Ductapemaster/HondaFitHDMI/wiki/hu_internals/original/pcb_audio_bottom.jpg

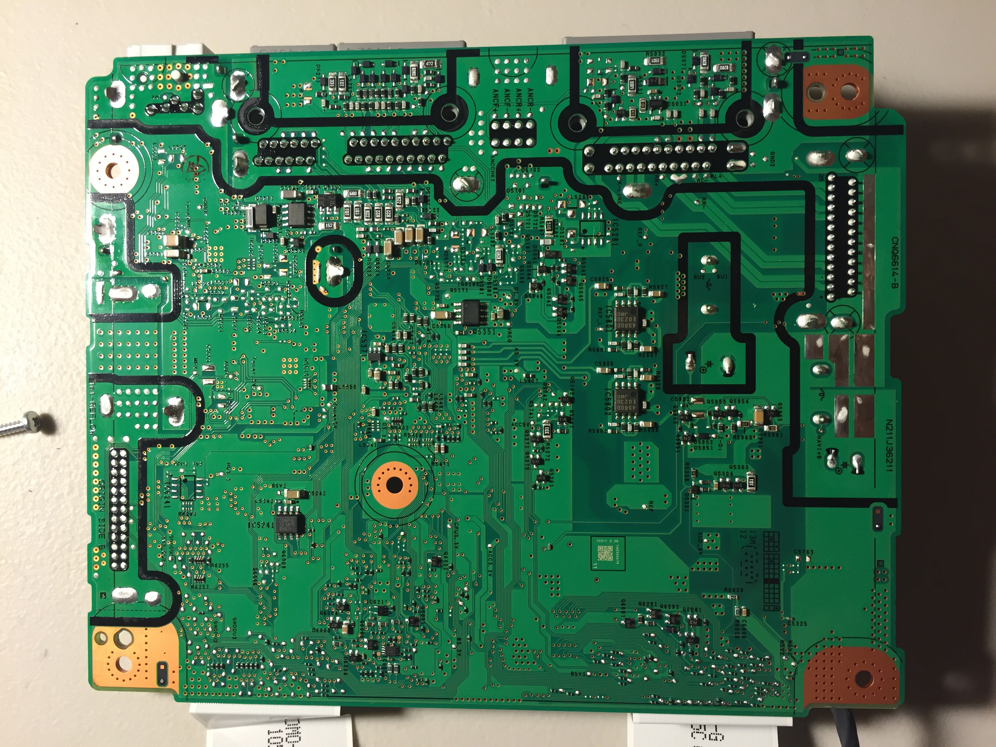
wiki/hu_internals/original/pcb_audio_bottom.jpg
