Ductapemaster/HondaFitHDMI/wiki/hu_internals/original/pcb_cpu_bottom.JPG

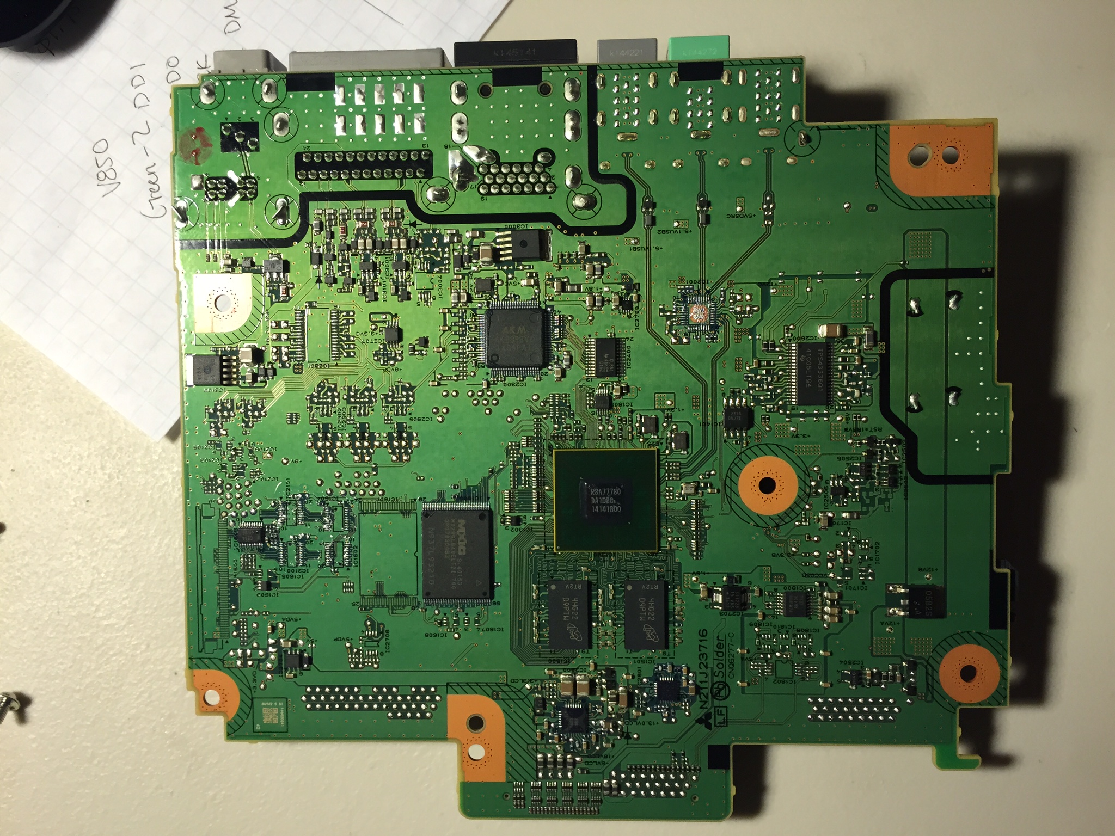
wiki/hu_internals/original/pcb_cpu_bottom.JPG
