Ductapemaster/HondaFitHDMI/wiki/hu_internals/original/pcb_cpu_top.JPG

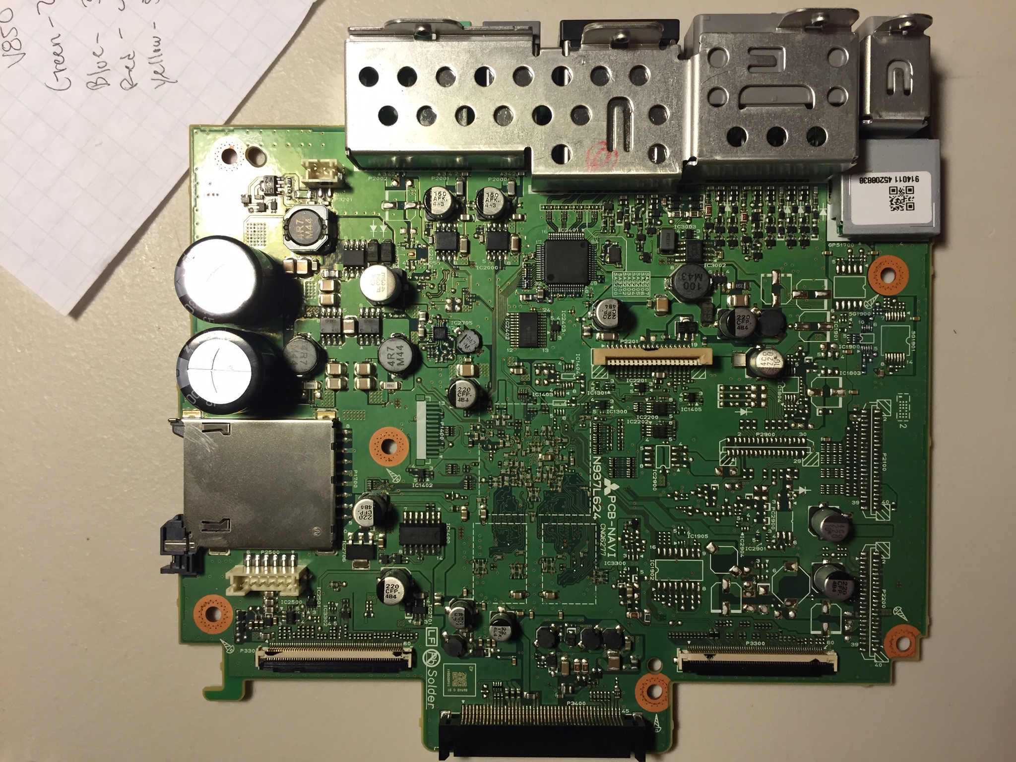
wiki/hu_internals/original/pcb_cpu_top.JPG
